imanolbarberia/3d-comp-drawers/renderer/2story_big.png

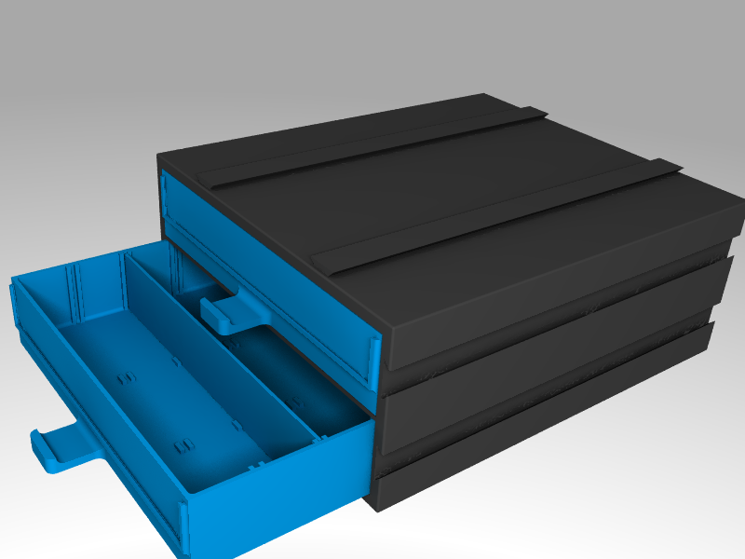
renderer/2story_big.png
