imanolbarberia/3d-comp-drawers/renderer/2story_tiny.png

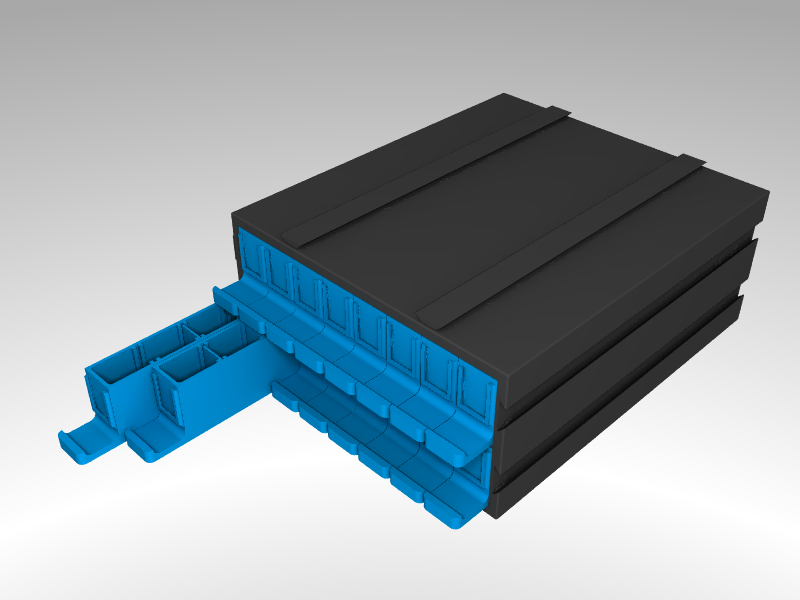
renderer/2story_tiny.png
