imanolbarberia/3d-comp-drawers/output/1story_drawer_small.stl

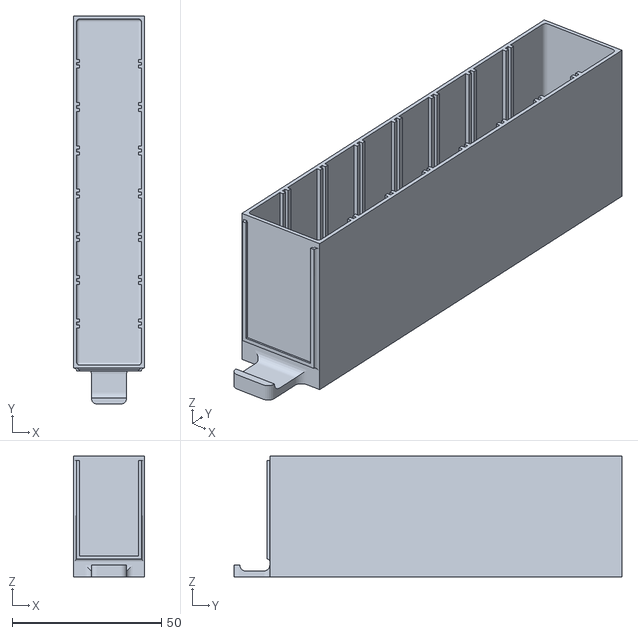
[picture p23: CAD file, 2019-05-25]
output/1story_drawer_small.stl
23.7 x 130.0 x 40.5
