imanolbarberia/3d-comp-drawers/output/1story_separator_standard.stl

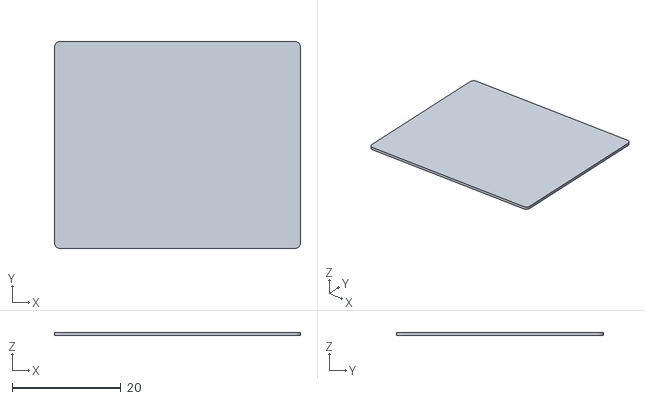
[picture p24: CAD file, 2019-05-25]
output/1story_separator_standard.stl
45.2 x 38.0 x 0.6
