imanolbarberia/3d-comp-drawers/output/2story_drawer_standard.stl

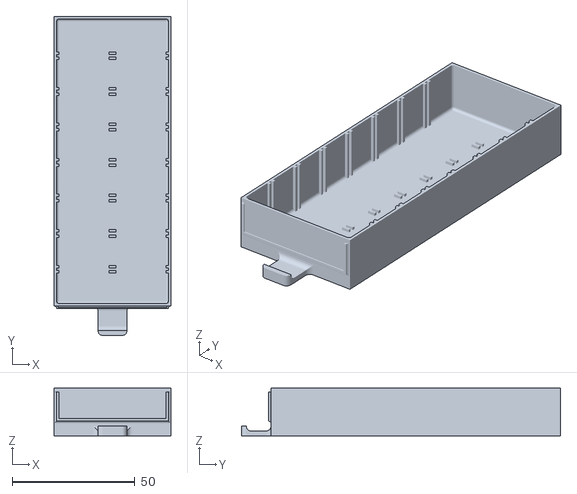
[picture p25: CAD file, 2019-05-24]
output/2story_drawer_standard.stl
47.6 x 130.0 x 19.5
