imanolbarberia/3d-comp-drawers/output/2story_drawer_small.stl

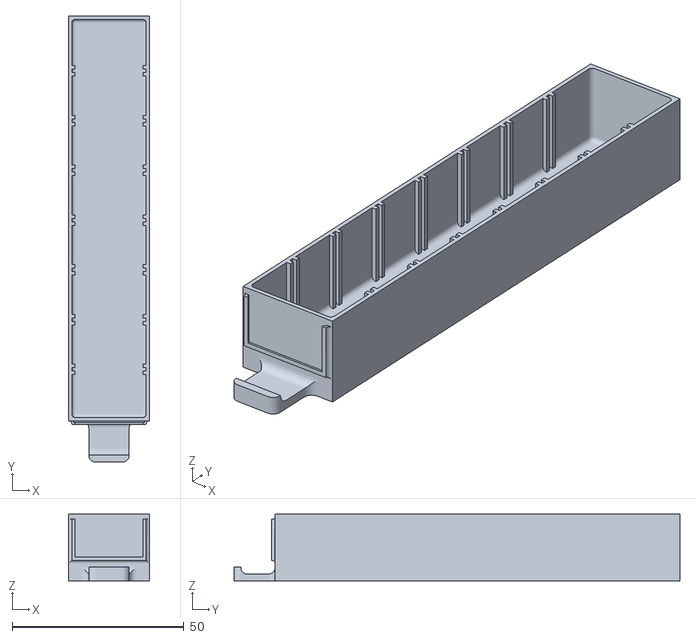
[picture p26: CAD file, 2019-05-24]
output/2story_drawer_small.stl
23.7 x 130.0 x 19.5
