imanolbarberia/3d-comp-drawers/output/2story_drawer_tiny.stl

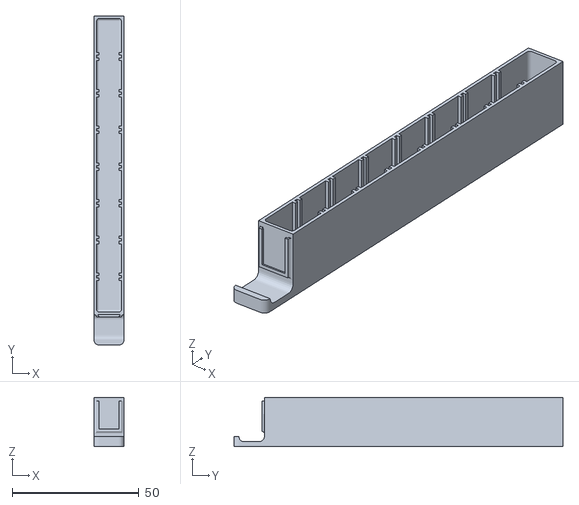
[picture p27: CAD file, 2019-05-24]
output/2story_drawer_tiny.stl
11.8 x 130.0 x 19.5
