imanolbarberia/3d-comp-drawers/output/2story_drawer_big.stl

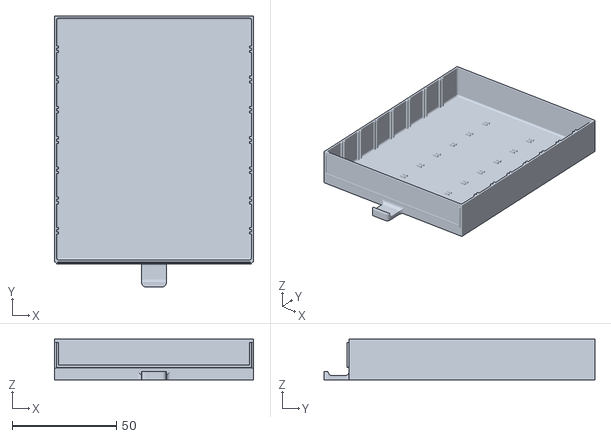
[picture p28: CAD file, 2019-05-24]
output/2story_drawer_big.stl
95.5 x 130.0 x 19.5
