imanolbarberia/3d-comp-drawers/output/2story_separator_standard.stl

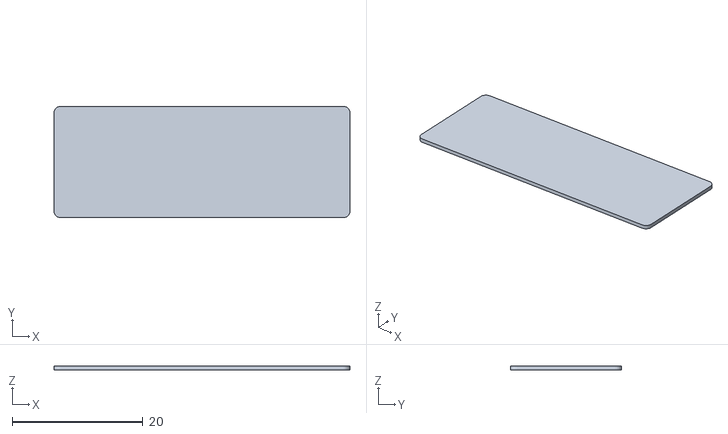
[picture p29: CAD file, 2018-05-02]
output/2story_separator_standard.stl
45.2 x 17.0 x 0.6
