imanolbarberia/3d-comp-drawers/output/2story_separator_big.stl

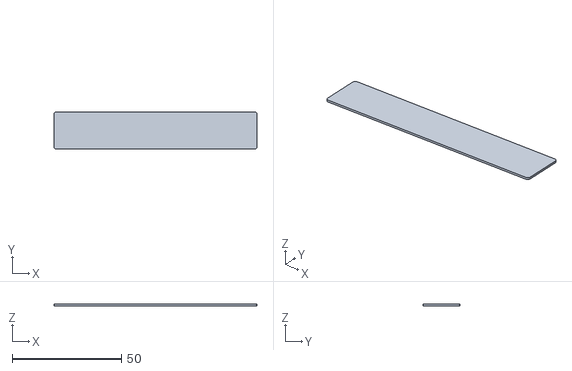
[picture p30: CAD file, 2018-05-02]
output/2story_separator_big.stl
93.1 x 17.0 x 0.8
