imanolbarberia/3d-comp-drawers/output/2story_separator_small.stl

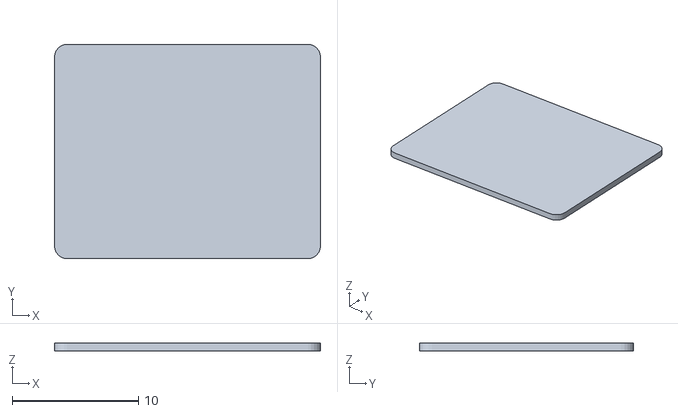
[picture p31: CAD file, 2018-04-25]
output/2story_separator_small.stl
21.1 x 17.0 x 0.6
