imanolbarberia/3d-comp-drawers/output/2story_separator_tiny.stl

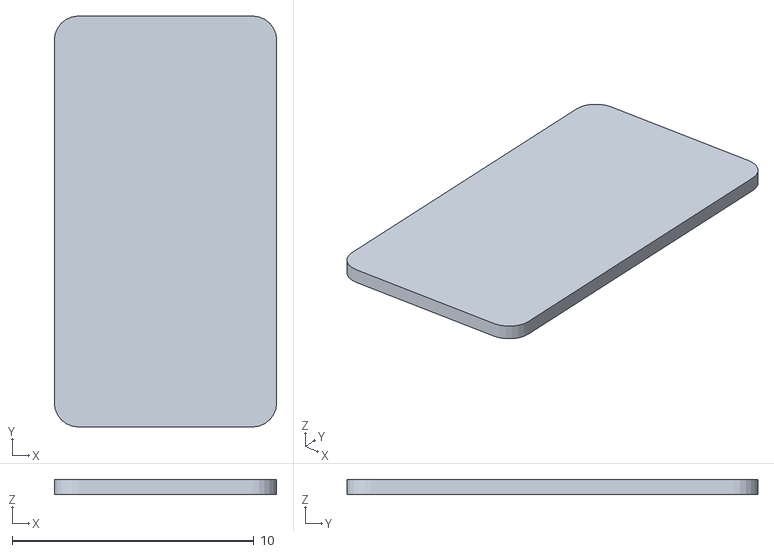
[picture p32: CAD file, 2018-04-25]
output/2story_separator_tiny.stl
9.20 x 17.0 x 0.6
